KomplexKapharnaum/KXKM_ESP32_Audio_Battery_hardware/Base_board/v3.2/mini-360-mp2307-1/MIni_3.png

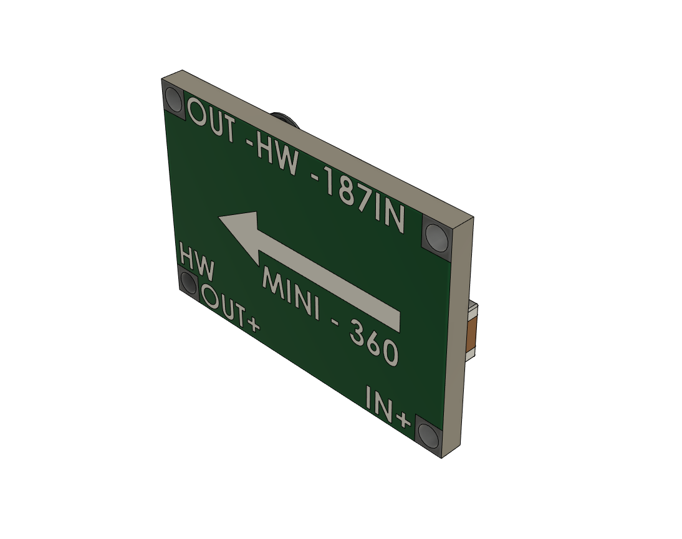
Base_board/v3.2/mini-360-mp2307-1/MIni_3.png
