KomplexKapharnaum/KXKM_ESP32_Audio_Battery_hardware/Base_board/v2/fab/KXKM_ESP32_battery_management_board_fab_top.pdf

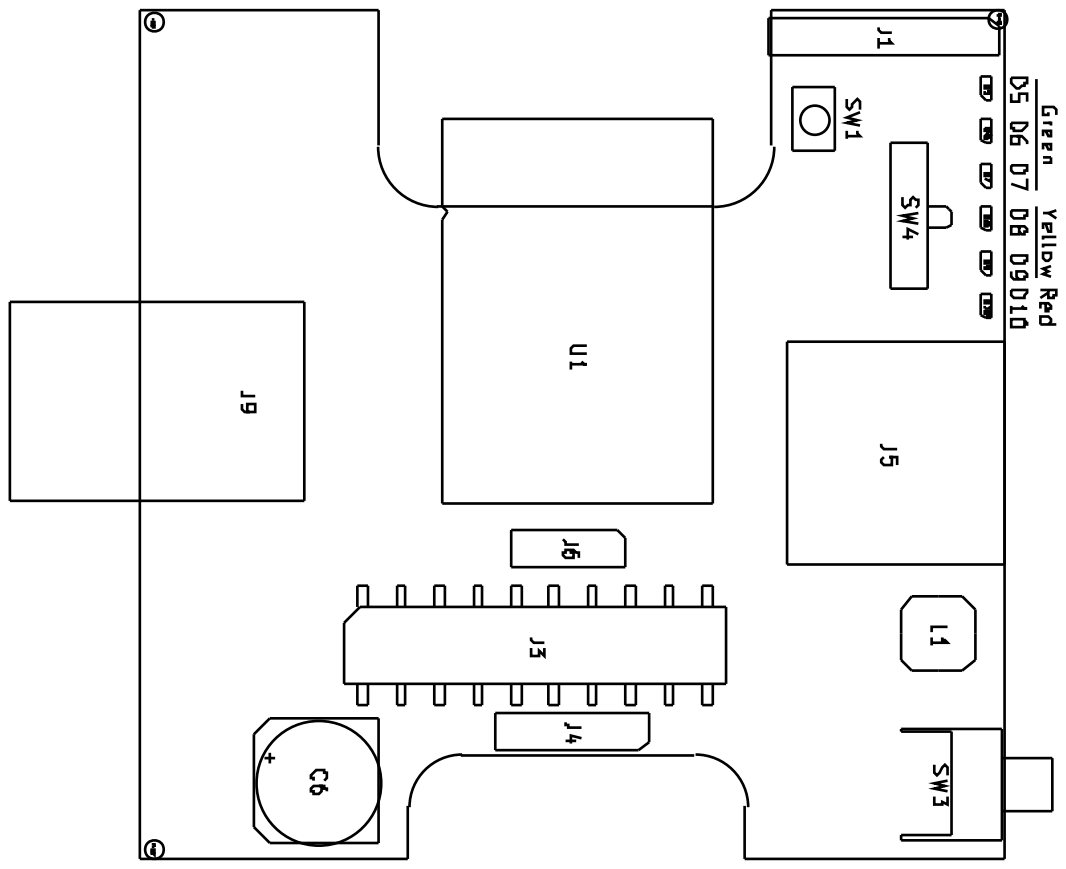
[picture p31: page 1]
